jcabetas/jaulaBack/version.h

/*
 * version.h
 *
 *  Created on: 16 ago 2023
 *      Author: joaquin
 *  from https://stackoverflow.com/questions/51727566/how-to-make-git-commit-hash-available-in-c-code-without-needless-recompiling
 */

#ifndef VERSION_H_
#define VERSION_H_

extern char const *const GIT_COMMIT;
extern char const *const GIT_TAG;

#endif /* VERSION_H_ */
